TollKit/tollkit/electronic_device/ultrasonic/script_ultrasonic.ino

int trig = 6;
int echo = 5;
int relay = 12;
int tiempo;
int distancia;
void setup() {
  pinMode(trig, OUTPUT);
  pinMode(echo, INPUT);
  pinMode(relay, OUTPUT);
}
void loop() {
  digitalWrite(trig, HIGH);
  delay(1);
  digitalWrite(trig, LOW);
  tiempo = pulseIn(echo, HIGH);
  distancia = tiempo / 58.2;
  if (distancia < 5){
    digitalWrite(relay, HIGH);
  }
  else{
    digitalWrite(relay, LOW);
  }
  delay(3000);
}
